Tinamous/OctoPrint-Badger/octoprint_Badger/nullTagReader.py

import logging
import logging.handlers

# Null tag reader that never returns a tag, used when no tag reader is available on the system
class NullTagReader():
	def __init__(self, logger):
		self._logger = logger

	def open(self, port):
		self._logger.info("Null tag reader open port: {0}".format(port))

	def close(self):
		self._logger.info("Null tag reader closing serial port")

	def read_version(self):
		return 1

	def seekTag(self):
		return None
